ChesterChenTW/Interactive-Glove-Puppetry-Device/Original CAD File/Solidworks 2018/controller_screw.SLDPRT

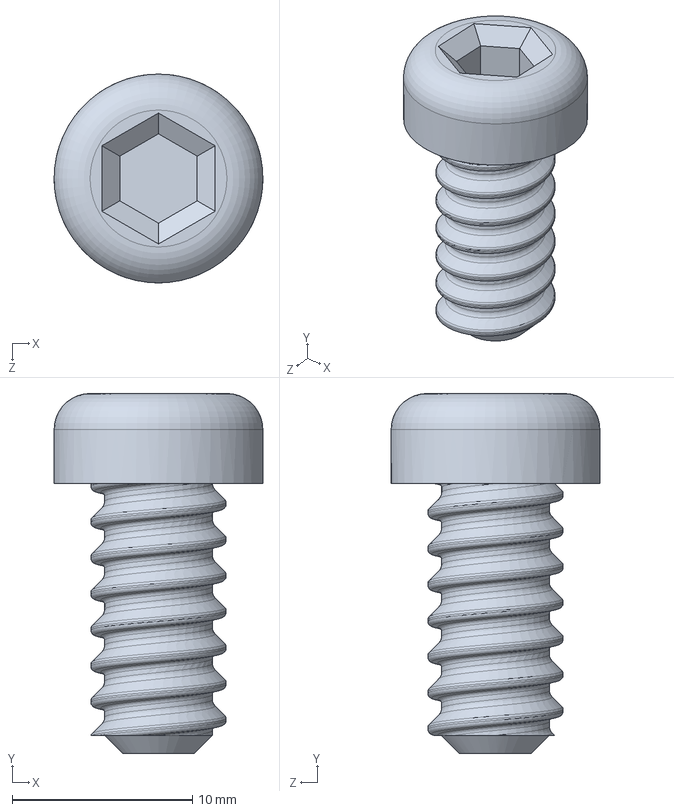
[picture p15: CAD file, 2022-07-11]
Original CAD File/Solidworks 2018/controller_screw.SLDPRT
11.6 x 20.0 x 11.6 mm
